hamano/musashi60/case/revE/thumb_plate.stl

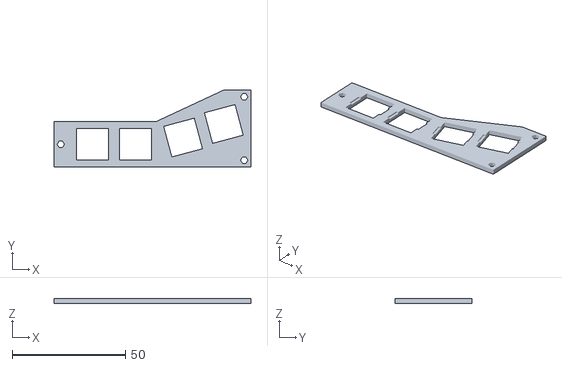
[picture p19: CAD file, 2022-02-08, an earlier design]
case/revE/thumb_plate.stl
87.0 x 34.0 x 2.00
