hamano/musashi60/case/revG/main_case.scad

use <main.scad>;

finger_case();
