hamano/musashi60/case/revG/main_plate.scad

use <main.scad>;

translate([0,-10])
rotate([180,0,0])
finger_plate();
