hamano/musashi60/case/revG/thumb.scad

use <common.scad>;

thumb_plate_points = [
                [2,  -26],
                [2,  -2],
                [82, -2],
                [98,-22],
                [82, -42],
                [68, -42],
                ];

thumb_plate_sc_points = [
                [2+4, -14],
                [82-2, -2-4],
                [71-2, -42+3],
                ];

module plate_nohole() {
    linear_extrude(height=2)
    polygon(points=thumb_plate_points);
}

module keyswitch_col(x=0,y=0,c=3,a=0) {
    translate([x,y])
    rotate([0,0,a])
    for (i = [0:c-1]) {
        keyswitch_hole(0, 19*i);
    }
}

module plate_holes() {
    keyswitch_hole(20, -14-3, 90);
    keyswitch_hole(39, -14, 90);
    keyswitch_hole(60, -16, 90-20);
    keyswitch_hole(78, -27, 90-40);

    for(p=thumb_plate_sc_points) {
        linear_extrude(height=5)
            translate(p)
            circle(1.6);
    }
}


module thumb_plate() {
    difference() {
        plate_nohole();
        plate_holes();
    }
}


tilt_angle = [10,15,0];
tilt_angle_r = tilt_angle * -1;
height = 36;

module thumb_case_outer_face() {
    projection()
        translate([0,0,height])
        rotate(tilt_angle)
        linear_extrude(height=2)
        offset(2)
        polygon(points=thumb_plate_points);
}

module thumb_case_inner_face() {
    projection()
        translate([0,0,height])
        rotate(tilt_angle)
        linear_extrude(height=2)
        offset(-2)
        polygon(points=thumb_plate_points);
}

module thumb_case_bottom_face() {
    difference(){
        thumb_case_outer_face();
        thumb_case_inner_face();
    }
    projection()
    translate([0,0,height])
    rotate(tilt_angle)
    for(p=thumb_plate_sc_points){
        linear_extrude(height=1)
        translate([-2,1])
        translate(p)
        circle(4);
    }
}

module case() {
    difference() {
        linear_extrude(height=50)
            thumb_case_bottom_face();
        translate([0,0,height])
            rotate(tilt_angle){
            linear_extrude(height=50)
                square(300, center=true);
            // screw hole
            translate([0,0,-9])
                linear_extrude(height=9)
                for(p=thumb_plate_sc_points){
                    translate(p)
                        circle(1.6);
                }
            // plate hole
            translate([0,0,-2])
            linear_extrude(height=2)
            offset(0.2)
            polygon(points=thumb_plate_points);
        }
    }
}

module thumb_case_hole(joint=true) {
    // cable hole
    translate([25,0,0])
    rotate([90,0,0])
    linear_extrude(height=4){
        translate([0, 15])
        circle(8);
        translate([-8,15])
        square([16, 30]);
    }
    if (joint) {
        for (x = [10,60]) {
            joint_female([x, 0]);
        }
    }
}

module thumb_case(joint=true) {
    difference() {
        case();
        thumb_case_hole(joint=joint);
    }
}

thumb_case();

translate([0, 60])
thumb_plate();
