hamano/musashi60/case/revG/thumb_case.scad

use <thumb.scad>;

thumb_case();
