hamano/musashi60/case/revG/thumb_plate.scad

use <thumb.scad>;

translate([0,10])
rotate([180,0,0])
thumb_plate();
