hamano/musashi60/case/revG/unit_case.scad

use <main.scad>;
use <thumb.scad>;

finger_case(joint=false);
translate([0,10])
thumb_case(joint=false);
