hamano/musashi60/qmk/musashi60.c

/* Copyright 2021 HAMANO Tsukasa
 *
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
 * You should have received a copy of the GNU General Public License
 * along with this program.  If not, see <http://www.gnu.org/licenses/>.
 */

#include "analog.h"
#include "print.h"
//#include "pointing_device.h"
#include "musashi60.h"

// Optional override functions below.
// You can leave any or all of these undefined.
// These are only required if you want to perform custom actions.
static int is_left;
static int is_master;

void keyboard_pre_init_kb(void) {
    debug_enable = true;
    debug_matrix = true;

    is_left = is_keyboard_left();
    is_master = is_keyboard_master();
}

void keyboard_post_init_kb(void) {
//    setPinOutput(GP25);
//    writePinHigh(GP25);

//    keyboard_post_init_user();
}

#ifdef POINTING_DEVICE_ENABLE

#define POINTING_H_PIN F4
#define POINTING_V_PIN F5
#define POINTING_S_PIN B5
#define POINTING_SPEED 6
#define POINTING_MAX ((1 << (9 - POINTING_SPEED)) - 1)

static report_mouse_t mouseReport = {};
static int8_t js_cal_x;
static int8_t js_cal_y;
static int no_js;


void pointing_device_init(void) {
    setPinInput(POINTING_H_PIN);
    setPinInput(POINTING_V_PIN);
    setPinInputHigh(POINTING_S_PIN);
    musashi60_calibration();
}

void musashi60_calibration() {
    int x = 0;
    int y = 0;
    int s = 0;
    dprintf("start calibration\n");
    for ( int i=0; i<10; i++) {
        x += analogReadPin(POINTING_H_PIN) >> 2;
        y += analogReadPin(POINTING_V_PIN) >> 2;
        s += readPin(POINTING_S_PIN);
    }
    x /= 10;
    y /= 10;
    dprintf("avg: %d, %d\n", x, y);
    js_cal_x = 127 - x;
    js_cal_y = 127 - y;
    dprintf("cal: %d, %d, %d\n", js_cal_x, js_cal_x, s);
    if ( s == 0 ) {
        no_js = s;
    }
}

void musashi60_set_mouse(uint8_t x, uint8_t y, uint8_t s) {
    mouseReport.x = ( x >> 3 ) - 16;
    mouseReport.y = ( y >> 3 ) - 16;
    if (mouseReport.x < 0) mouseReport.x++;
    if (mouseReport.y < 0) mouseReport.y++;
    if (mouseReport.x || mouseReport.y ) {
        dprintf("set_mouse: %d, %d, %d\n", mouseReport.x, mouseReport.y, s);
        pointing_device_set_report(mouseReport);
    }
}

void musashi60_set_wheel(uint8_t x, uint8_t y) {
    mouseReport.h = ( x >> 6 ) - 2;
    mouseReport.v = ( y >> 6 ) - 2;
    if (mouseReport.h < 0) mouseReport.h++;
    if (mouseReport.v < 0) mouseReport.v++;
    mouseReport.v *= -1;
    if ( mouseReport.h || mouseReport.v ) {
        dprintf("set_wheel: %d\n", mouseReport.v);
        pointing_device_set_report(mouseReport);
    }
}

void pointing_device_task(void) {
    uint8_t x, y, s = 0;
    if ( no_js ) {
        return;
    }
    x = (analogReadPin(POINTING_H_PIN) >> 2) + js_cal_x; // adjust center=127
    y = (analogReadPin(POINTING_V_PIN) >> 2) + js_cal_y; // adjust center=127
    s = readPin(POINTING_S_PIN);
    uprintf("d x, y, no_js: %d, %d, %d\n", x, y, s);
    //dprintf("d x, y: %d, %d\n", x, y);
    if ( is_master ) {
        musashi60_set_mouse(x, y, s);
    } else {
        musashi60_send_axis(x, y);
    }
    pointing_device_send();
}

#endif

/*
void matrix_init_kb(void) {
    // put your keyboard start-up code here
    // runs once when the firmware starts up

    matrix_init_user();
}

void matrix_scan_kb(void) {
    // put your looping keyboard code here
    // runs every cycle (a lot)

    matrix_scan_user();
}

bool process_record_kb(uint16_t keycode, keyrecord_t *record) {
    // put your per-action keyboard code here
    // runs for every action, just before processing by the firmware

    return process_record_user(keycode, record);
}

bool led_update_kb(led_t led_state) {
    // put your keyboard LED indicator (ex: Caps Lock LED) toggling code here

    return led_update_user(led_state);
}
*/
