hamano/musashi60/qmk/musashi60.h

/* Copyright 2021 HAMANO Tsukasa
 *
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
 * You should have received a copy of the GNU General Public License
 * along with this program.  If not, see <http://www.gnu.org/licenses/>.
 */

#pragma once

#include "quantum.h"

/* This is a shortcut to help you visually see your layout.
 *
 * The first section contains all of the arguments representing the physical
 * layout of the board and position of the keys.
 *
 * The second converts the arguments into a two-dimensional array which
 * represents the switch matrix.
 */

#define XXX KC_NO

#define LAYOUT( \
    LG1, LF1, LE1, LD1, LC1, LB1,           RB1, RC1, RD1, RE1, RF1, RG1, \
    LG2, LF2, LE2, LD2, LC2, LB2, LA2, RA2, RB2, RC2, RD2, RE2, RF2, RG2, \
    LG3, LF3, LE3, LD3, LC3, LB3, LA3, RA3, RB3, RC3, RD3, RE3, RF3, RG3, \
    LG4, LF4, LE4, LD4, LC4, LB4,           RB4, RC4, RD4, RE4, RF4, RG4, \
                   LD5, LC5, LB5, LA5, RA5, RB5, RC5, RD5                 \
) \
{ \
    { XXX, LB1, LC1, LD1, LE1, LF1, LG1 }, \
    { LA2, LB2, LC2, LD2, LE2, LF2, LG2 }, \
    { LA3, LB3, LC3, LD3, LE3, LF3, LG3 }, \
    { XXX, LB4, LC4, LD4, LE4, LF4, LG4 }, \
    { LA5, LB5, LC5, LD5, XXX, XXX, XXX }, \
    { XXX, RB1, RC1, RD1, RE1, RF1, RG1 }, \
    { RA2, RB2, RC2, RD2, RE2, RF2, RG2 }, \
    { RA3, RB3, RC3, RD3, RE3, RF3, RG3 }, \
    { XXX, RB4, RC4, RD4, RE4, RF4, RG4 }, \
    { RA5, RB5, RC5, RD5, XXX, XXX, XXX }  \
}

void musashi60_calibration(void);
void musashi60_send_axis(uint8_t x, uint8_t y);
void musashi60_set_mouse(uint8_t x, uint8_t y, uint8_t s);
void musashi60_set_wheel(uint8_t x, uint8_t y);
